Randagodron/harmonic-jerkulator/export/harmonic_jerkulator_finished_01.jpg

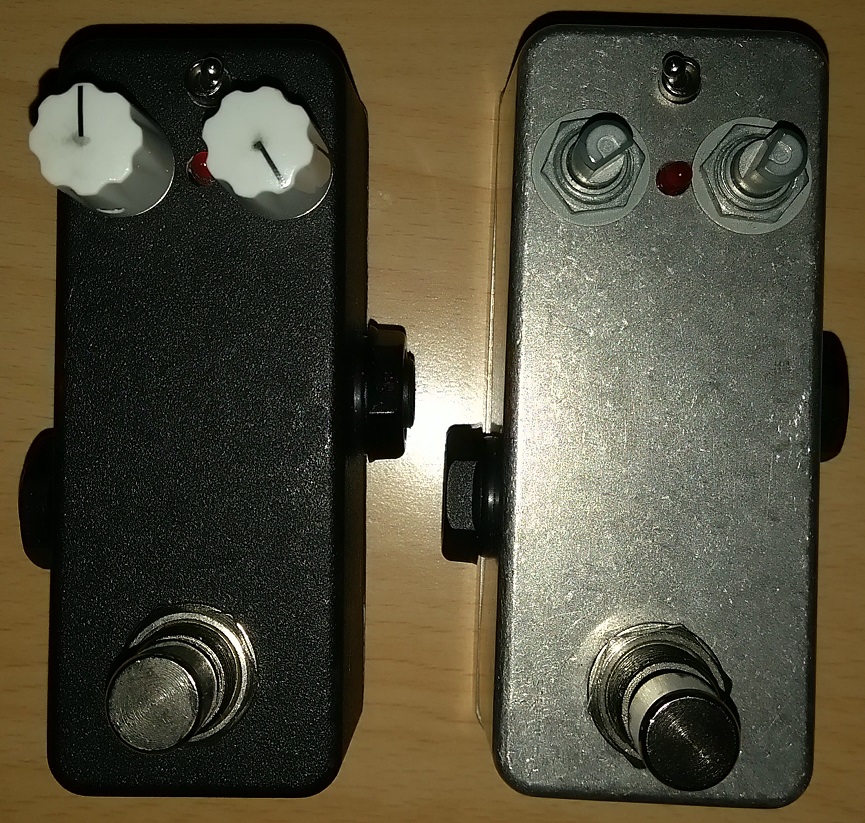
export/harmonic_jerkulator_finished_01.jpg
