Randagodron/harmonic-jerkulator/export/harmonic_jerkulator_finished_03.jpg

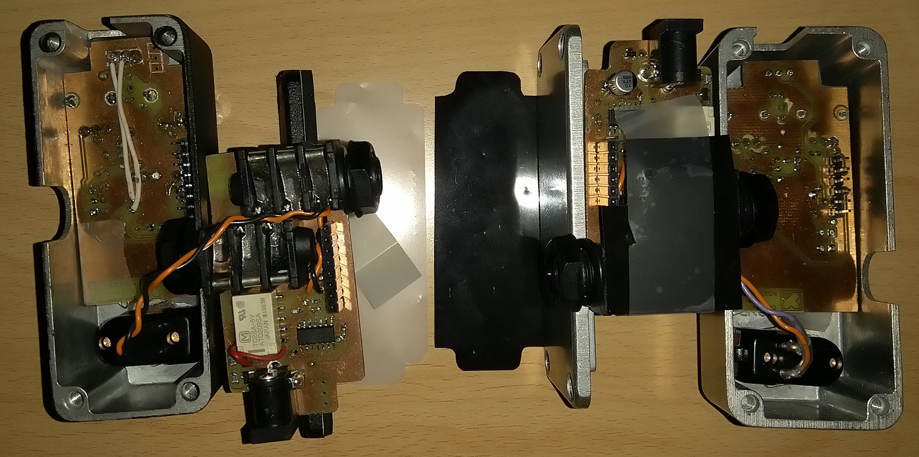
export/harmonic_jerkulator_finished_03.jpg
