Randagodron/harmonic-jerkulator/export/harmonic_jerkulator_finished_04.jpg

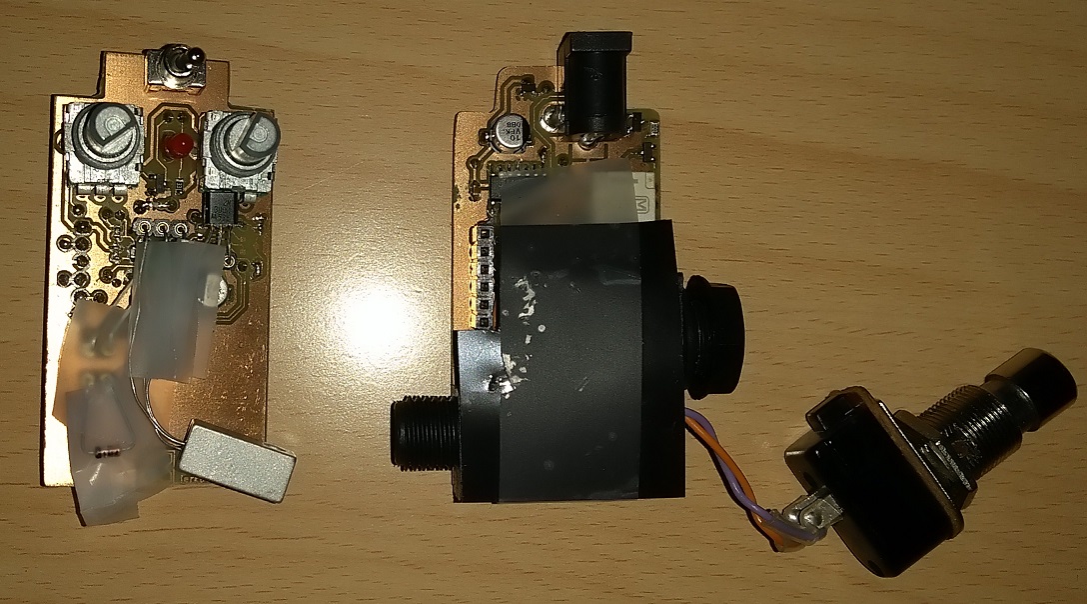
export/harmonic_jerkulator_finished_04.jpg
