Randagodron/harmonic-jerkulator/export/harmonic_jerkulator_finished_06.jpg

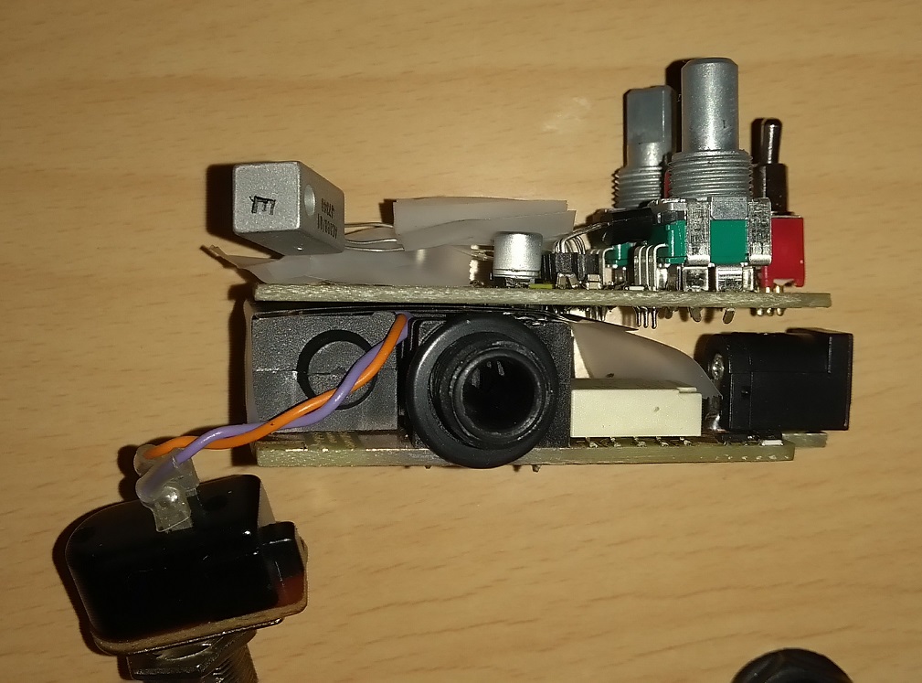
export/harmonic_jerkulator_finished_06.jpg
