Randagodron/harmonic-jerkulator/export/spice_graph_02.PNG

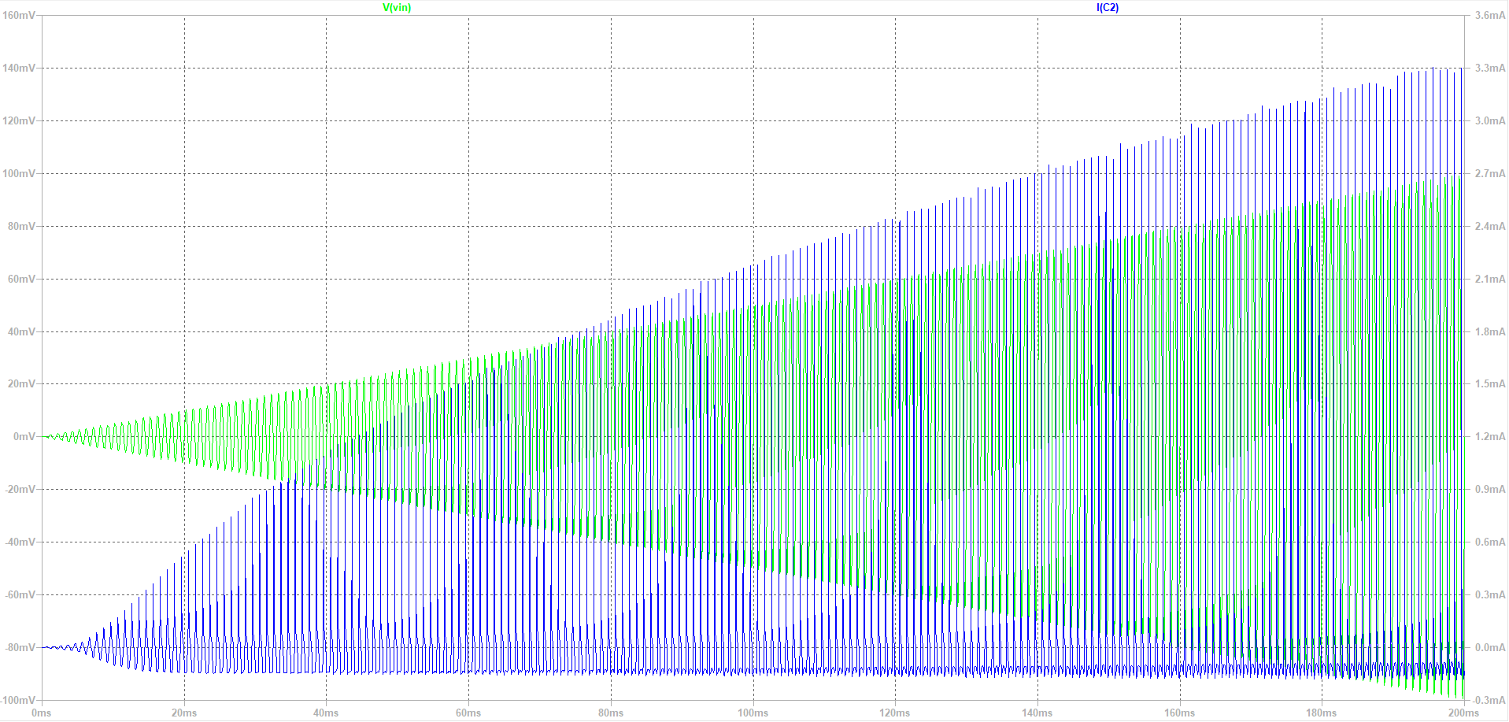
export/spice_graph_02.PNG
