Randagodron/harmonic-jerkulator/export/spice_graph_03.PNG

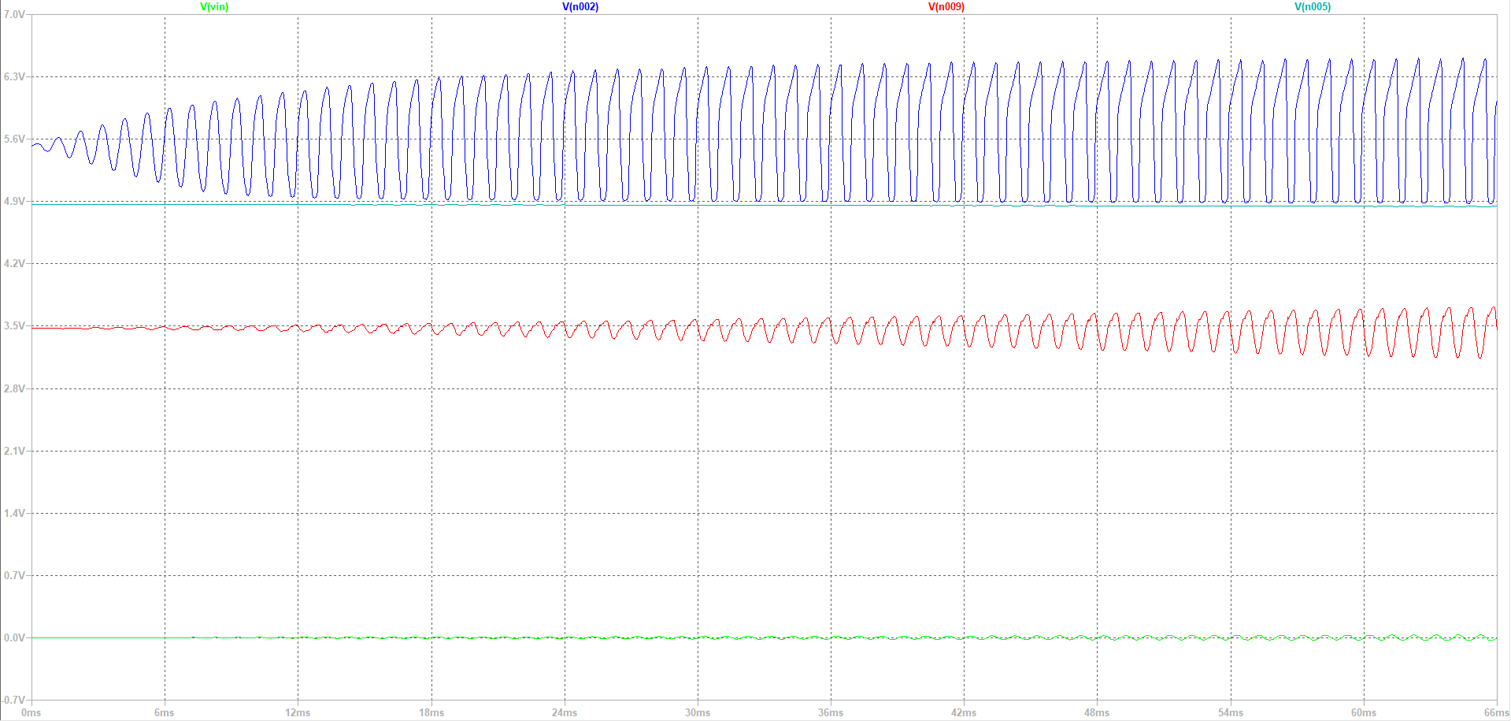
export/spice_graph_03.PNG
