Randagodron/harmonic-jerkulator/export/spice_sch_01.PNG

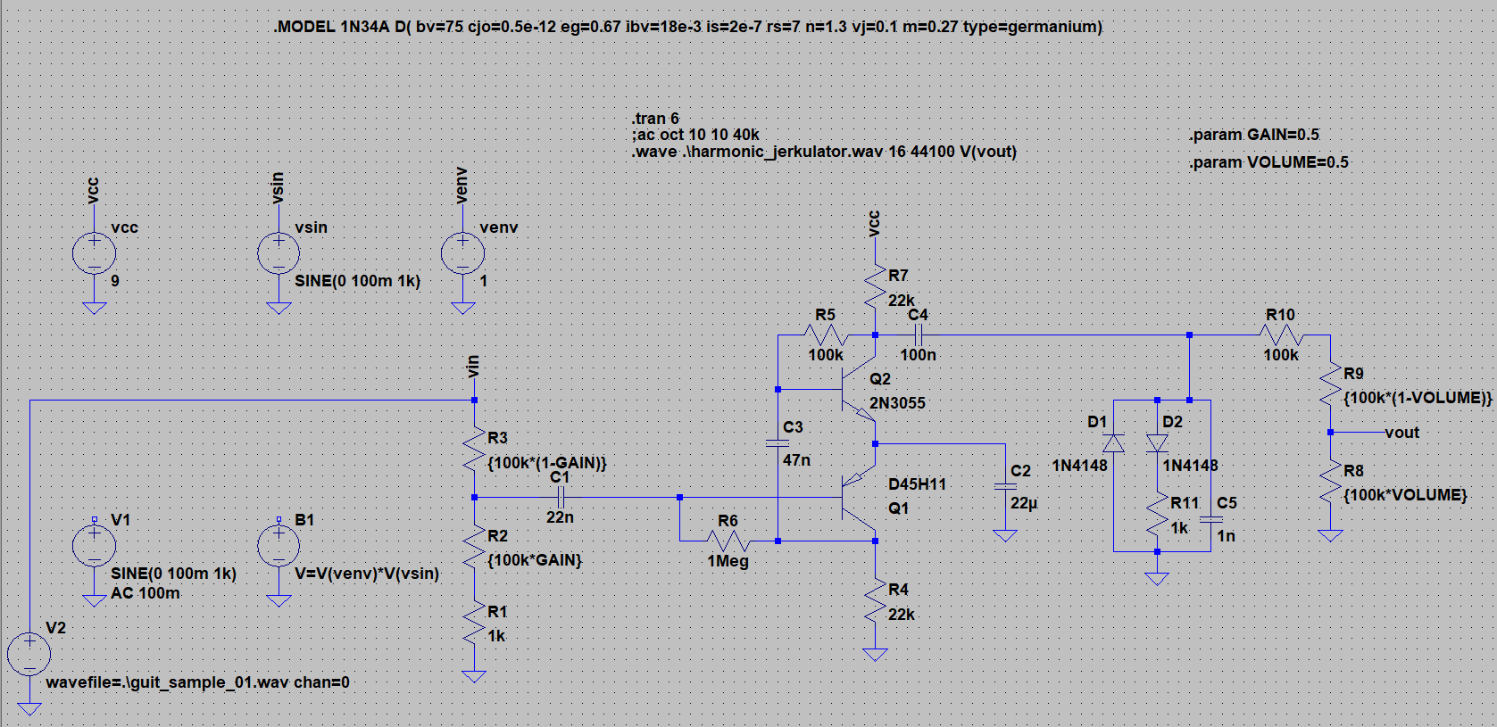
export/spice_sch_01.PNG
