Randagodron/harmonic-jerkulator/export/spice_sch_02.PNG

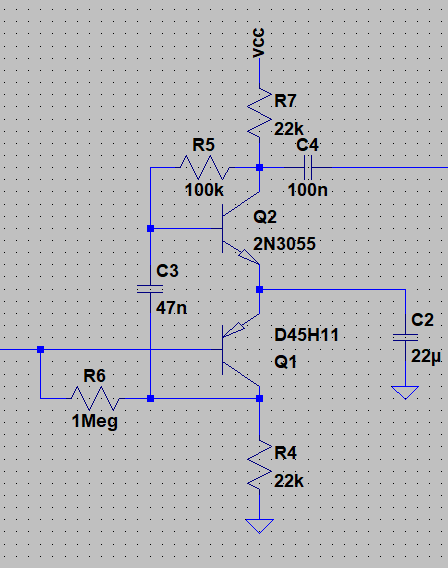
export/spice_sch_02.PNG
