Randagodron/harmonic-jerkulator/sim/harmonic_jerkulator_01.asc

B1: bv; V=V(venv)*V(vsin)
C1: cap; 22n
C2: cap; 22µ
C3: cap; 47n
C4: cap; 100n
C5: cap; 1n
D1: diode; 1N4148
D2: diode; 1N4148
Q1: pnp; 2N3906
Q2: npn; 2N3904
R1: res; 1k
R2: res; {100k*GAIN}
R3: res; {100k*(1-GAIN)}
R4: res; 22k
R5: res; 100k
R6: res; 1Meg
R7: res; 22k
R8: res; {100k*VOLUME}
R9: res; {100k*(1-VOLUME)}
R10: res; 100k
R11: res; 1k
V1: voltage; SINE(0 100m 1k); AC 100m
V2: voltage; wavefile=.\guit_sample_01.wav chan=0
vcc: voltage; 9
venv: voltage; 1
vsin: voltage; SINE(0 100m 1k)
Named nets: 0, vcc, vsin, venv, vout, vin
.param GAIN=0.5
.param VOLUME=0.5
.tran 6
;ac oct 10 10 40k
.wave .\\harmonic_jerkulator.wav 16 44100 V(vout)
.MODEL 1N34A D( bv=75 cjo=0.5e-12 eg=0.67 ibv=18e-3 is=2e-7 rs=7 n=1.3 vj=0.1 m=0.27 type=germanium)
.op
